17jmcl/PhotoSynth_1.0/Code/PlantSynth_01/PlantSynth_Piano.h

#ifndef PlantSynth_Piano_h
#define PlantSynth_Piano_h

#include "Arduino.h"
#include "AudioStream.h"

class PlantSynthPiano
{
      public:
      void pianoSetup();
      void mixGainSetup();
      void setPianoHz();
      void setWaveForm();
      void playKey();
      int currWave();
};

#endif
