17jmcl/PhotoSynth_1.0/Code/PlantSynth_01/PlantSynth_bitcrusher.h

#ifndef PlantSynth_bitcrusher_h
#define PlantSynth_bitcrusher_h

#include "Arduino.h" 
#include <Bounce2.h>

class bitCrusher
{
      public:
      void updatebitcrush();
      void buttonpress();
      float updateknob(float x);
      float updateknob2(float y);
};

#endif
